charlesvestal/owntone-nfc/tests/test_controller.py

import datetime

import httpx
import pytest

from nfc_jukebox.cards import Card
from nfc_jukebox.config import Config
from nfc_jukebox.controller import Controller, State
from nfc_jukebox.owntone import is_airplay, is_local


class FakeClock:
    def __init__(self) -> None:
        self.now = 1000.0

    def __call__(self) -> float:
        return self.now

    def advance(self, seconds: float) -> None:
        self.now += seconds


class FakeWallClock:
    """The *second* time source: local wall-clock time, for "has 3am happened".

    Separate from FakeClock on purpose, exactly as in the controller: durations
    are measured on the monotonic clock, and only the question "which side of
    the reset hour are we on" is asked of this one. Tests drive it explicitly
    so nothing has to sleep or move the machine's clock.
    """

    def __init__(self, at: str = "2026-09-18 20:00") -> None:
        self.now = datetime.datetime.fromisoformat(at)

    def __call__(self) -> datetime.datetime:
        return self.now

    def set(self, at: str) -> None:
        self.now = datetime.datetime.fromisoformat(at)


class FakeOwnTone:
    """A stand-in for the REST client.

    The `type` strings are OwnTone's real ones, and the classification
    predicates are imported from the production module rather than re-guessed
    here: fakes that reimplement the thing under test are how the AirPlay
    release bug survived a green suite.
    """

    def __init__(self) -> None:
        self.calls: list[tuple] = []
        self.outputs = [
            {"id": "1", "type": "ALSA", "selected": True},
            {"id": "2", "type": "AirPlay 2", "selected": False},
        ]
        # The queue and the transport state are modelled because the resume
        # rule depends on both: the position lives in OwnTone's queue, and
        # "the side has run out" is only visible as the player stopping.
        self.queue = 0
        self.player = "stop"
        # Which album the queue holds, so a restart can recognise it.
        self.queue_album: str | None = None

    def _ids(self, predicate):
        return [o["id"] for o in self.outputs if predicate(o)]

    def selected_output_ids(self):
        return self._ids(lambda o: o["selected"])

    def airplay_output_ids(self):
        return self._ids(is_airplay)

    def local_output_ids(self):
        return self._ids(is_local)

    def all_output_ids(self):
        return self._ids(lambda o: True)

    def set_vinyl_playback_mode(self):
        self.calls.append(("set_vinyl_playback_mode",))

    def set_outputs(self, ids):
        self.calls.append(("set_outputs", tuple(ids)))
        for o in self.outputs:
            o["selected"] = o["id"] in ids

    def play_album(self, path):
        self.calls.append(("play_album", path))
        self.queue = 12
        self.queue_album = path
        self.player = "play"

    def play(self):
        self.calls.append(("play",))
        self.player = "play"

    def pause(self):
        self.calls.append(("pause",))
        self.player = "pause"

    def stop(self):
        self.calls.append(("stop",))
        self.player = "stop"

    def clear_queue(self):
        self.calls.append(("clear_queue",))
        self.queue = 0
        self.queue_album = None
        self.player = "stop"

    def queue_length(self):
        self.calls.append(("queue_length",))
        return self.queue

    def player_state(self):
        return {"state": self.player}

    def queue_holds_album(self, relative_path):
        return self.queue > 0 and self.queue_album == relative_path

    def finish_album(self):
        """What OwnTone looks like when the last track has played out."""
        self.player = "stop"


class FakeCards:
    def __init__(self, mapping):
        self._mapping = mapping

    def get(self, uid):
        return self._mapping.get(uid)


class FakeSnapshot:
    def __init__(self, initial=None):
        self.value = initial or []

    def load(self):
        return list(self.value)

    def save(self, ids):
        self.value = list(ids)


@pytest.fixture
def wall():
    return FakeWallClock()


@pytest.fixture
def ctx(wall):
    clock = FakeClock()
    owntone = FakeOwnTone()
    cards = FakeCards({
        "aaaa": Card(uid="aaaa", name="Blue", path="Miles Davis/Kind of Blue"),
        "bbbb": Card(uid="bbbb", name="Rumours", path="Fleetwood Mac/Rumours"),
        # Only ever used by _prime, which has to leave a *different* record on
        # the platter from the one the test under way is about.
        "cccc": Card(uid="cccc", name="Primer", path="Various/Primer"),
    })
    snapshot = FakeSnapshot()
    config = Config(grace_period_s=90.0)
    controller = Controller(owntone, cards, snapshot, config,
                            clock=clock, wall_clock=wall)
    return controller, owntone, snapshot, clock


def test_card_placed_starts_album(ctx):
    controller, owntone, _, _ = ctx
    controller.on_card_present("aaaa")
    assert ("play_album", "Miles Davis/Kind of Blue") in owntone.calls
    assert controller.state is State.PLAYING


def test_card_removed_pauses_immediately(ctx):
    controller, owntone, _, _ = ctx
    controller.on_card_present("aaaa")
    controller.on_card_removed()
    assert owntone.calls[-1] == ("pause",)
    assert controller.state is State.PAUSED


def test_same_card_replaced_at_once_resumes(ctx):
    controller, owntone, _, clock = ctx
    controller.on_card_present("aaaa")
    controller.on_card_removed()
    clock.advance(0.2)
    controller.on_card_present("aaaa")
    assert owntone.calls[-1] == ("play",)
    album_calls = [c for c in owntone.calls if c[0] == "play_album"]
    assert album_calls == [("play_album", "Miles Davis/Kind of Blue")]


def test_same_card_resumes_however_long_it_has_been_off(ctx):
    """Lifting a card is how you pause a record player, and pausing must not
    lose your place. The record stays on the platter until a different one is
    put on - so there is no window after which the same card starts over."""
    controller, owntone, _, clock = ctx
    controller.on_card_present("aaaa")
    controller.on_card_removed()
    clock.advance(3600.0)
    controller.tick()  # grace expired long ago; the outputs were released
    controller.on_card_present("aaaa")
    assert sum(1 for c in owntone.calls if c[0] == "play_album") == 1
    assert owntone.calls[-1] == ("play",)
    assert controller.state is State.PLAYING
    assert controller.now_playing == "Blue"


def test_a_resume_after_a_release_re_selects_the_speakers(ctx):
    """The release handed the HomePods back, so a resume has to take them
    again - otherwise the record comes back out of the wrong speaker."""
    controller, owntone, snapshot, clock = ctx
    _prime(controller, owntone, snapshot, clock)
    snapshot.save(["1", "2"])
    controller.on_card_present("aaaa")
    assert owntone.selected_output_ids() == ["1", "2"]

    controller.on_card_removed()
    clock.advance(91.0)
    controller.tick()
    assert owntone.selected_output_ids() == ["1"]  # HomePod handed back

    controller.on_card_present("aaaa")
    assert owntone.selected_output_ids() == ["1", "2"]
    assert controller.state is State.PLAYING


def test_different_card_switches_immediately(ctx):
    controller, owntone, _, _ = ctx
    controller.on_card_present("aaaa")
    controller.on_card_present("bbbb")
    assert ("play_album", "Fleetwood Mac/Rumours") in owntone.calls


def test_a_different_card_starts_from_track_one_not_where_it_left_off(ctx):
    """Only one record is on the platter at a time. Putting a different one on
    is what ends the first one's place."""
    controller, owntone, _, clock = ctx
    controller.on_card_present("aaaa")
    controller.on_card_removed()
    clock.advance(91.0)
    controller.tick()

    controller.on_card_present("bbbb")
    assert ("play_album", "Fleetwood Mac/Rumours") in owntone.calls

    controller.on_card_removed()
    clock.advance(91.0)
    controller.tick()
    owntone.calls.clear()

    controller.on_card_present("aaaa")  # back to the first record
    assert ("play_album", "Miles Davis/Kind of Blue") in owntone.calls
    assert ("play",) not in owntone.calls


def test_grace_expiry_releases_airplay_without_losing_the_place(ctx):
    """Releasing the speakers is the part that matters: the HomePods must go
    idle and become available to other senders. Stopping and clearing the
    queue would throw the position away, and the position is the whole point
    of the pause."""
    controller, owntone, _, clock = ctx
    owntone.outputs[1]["selected"] = True  # AirPlay selected
    controller.on_card_present("aaaa")
    controller.on_card_removed()
    clock.advance(91.0)
    controller.tick()
    assert owntone.selected_output_ids() == ["1"]  # AirPlay deselected
    assert ("stop",) not in owntone.calls
    assert ("clear_queue",) not in owntone.calls
    assert owntone.queue == 12  # the album is still loaded
    assert controller.state is State.IDLE


def test_a_finished_album_starts_over_on_the_next_tap(ctx):
    """A record that played its last groove has no place left to hold."""
    controller, owntone, _, clock = ctx
    controller.on_card_present("aaaa")

    owntone.finish_album()
    clock.advance(30.0)
    controller.tick()

    controller.on_card_removed()
    clock.advance(91.0)
    controller.tick()
    owntone.calls.clear()

    controller.on_card_present("aaaa")
    assert ("play_album", "Miles Davis/Kind of Blue") in owntone.calls
    assert ("play",) not in owntone.calls


def test_a_paused_album_is_not_mistaken_for_a_finished_one(ctx):
    """OwnTone reports `pause` for a card lifted mid-track and `stop` only
    when the queue has run out. Confusing the two would throw the place away
    on every lift."""
    controller, owntone, _, clock = ctx
    controller.on_card_present("aaaa")
    controller.on_card_removed()
    assert owntone.player_state()["state"] == "pause"
    clock.advance(30.0)
    controller.tick()
    owntone.calls.clear()

    controller.on_card_present("aaaa")
    assert ("play",) in owntone.calls
    assert not any(c[0] == "play_album" for c in owntone.calls)


def test_the_finished_check_is_not_run_on_every_tick(ctx):
    controller, owntone, _, clock = ctx
    controller.on_card_present("aaaa")
    polls = []
    owntone.player_state = lambda: (polls.append(1), {"state": "play"})[1]
    for _ in range(10):
        clock.advance(1.0)
        controller.tick()
    assert len(polls) <= 1


def test_a_stale_loaded_album_does_not_resume_into_an_empty_queue(ctx):
    """OwnTone restarting under us empties the queue while our memory of what
    is loaded survives. Resuming then would be silence, so the check is what
    OwnTone actually has, not what we remember."""
    controller, owntone, _, clock = ctx
    controller.on_card_present("aaaa")
    controller.on_card_removed()
    clock.advance(91.0)
    controller.tick()

    owntone.queue = 0  # OwnTone restarted; the queue went with it
    owntone.calls.clear()

    controller.on_card_present("aaaa")
    assert ("play_album", "Miles Davis/Kind of Blue") in owntone.calls
    assert controller.state is State.PLAYING


def test_a_failed_queue_check_starts_the_album_rather_than_risking_silence(ctx):
    controller, owntone, _, clock = ctx
    controller.on_card_present("aaaa")
    controller.on_card_removed()
    clock.advance(91.0)
    controller.tick()
    owntone.queue_length = _boom
    owntone.calls.clear()

    controller.on_card_present("aaaa")
    assert ("play_album", "Miles Davis/Kind of Blue") in owntone.calls
    assert controller.state is State.PLAYING


# --- start over ------------------------------------------------------------


def test_start_over_restarts_the_loaded_album(ctx):
    controller, owntone, _, clock = ctx
    controller.on_card_present("aaaa")
    controller.on_card_removed()
    clock.advance(91.0)
    controller.tick()
    owntone.calls.clear()

    assert controller.start_over() == "Blue"

    assert ("play_album", "Miles Davis/Kind of Blue") in owntone.calls
    assert controller.state is State.PLAYING
    assert controller.now_playing == "Blue"


def test_start_over_re_selects_the_speakers_too(ctx):
    controller, owntone, snapshot, clock = ctx
    _prime(controller, owntone, snapshot, clock)
    snapshot.save(["1", "2"])
    controller.on_card_present("aaaa")
    controller.on_card_removed()
    clock.advance(91.0)
    controller.tick()
    assert owntone.selected_output_ids() == ["1"]

    controller.start_over()

    assert owntone.selected_output_ids() == ["1", "2"]


def test_start_over_with_nothing_loaded_says_so(ctx):
    controller, owntone, _, _ = ctx
    with pytest.raises(LookupError):
        controller.start_over()
    assert not any(c[0] == "play_album" for c in owntone.calls)


def test_start_over_after_a_finished_album_has_nothing_to_restart(ctx):
    controller, owntone, _, clock = ctx
    controller.on_card_present("aaaa")
    owntone.finish_album()
    clock.advance(30.0)
    controller.tick()
    with pytest.raises(LookupError):
        controller.start_over()


def test_start_over_surfaces_an_owntone_failure(ctx):
    controller, owntone, _, _ = ctx
    controller.on_card_present("aaaa")
    owntone.play_album = _boom
    with pytest.raises(RuntimeError):
        controller.start_over()
    assert controller.last_error is not None


def test_start_over_mid_album_does_not_need_the_card_lifted(ctx):
    controller, owntone, _, _ = ctx
    controller.on_card_present("aaaa")
    owntone.calls.clear()
    controller.start_over()
    assert ("play_album", "Miles Davis/Kind of Blue") in owntone.calls
    assert controller.state is State.PLAYING


# --- the nightly reset -----------------------------------------------------
#
# An album left unfinished at midnight should not still be waiting mid-side at
# lunchtime the next day. The reset hour is a wall-clock question, which is why
# the controller carries a second, separate time source: the monotonic clock
# cannot answer "has 3am happened", and the wall clock must never be used for
# the grace period, where an NTP step would strand a paused card.


def test_an_album_loaded_last_night_starts_fresh_after_the_reset_hour(ctx, wall):
    controller, owntone, _, clock = ctx
    wall.set("2026-09-18 23:00")
    controller.on_card_present("aaaa")
    controller.on_card_removed()
    clock.advance(91.0)
    controller.tick()
    owntone.calls.clear()

    wall.set("2026-09-19 10:00")  # 3am has been and gone
    controller.on_card_present("aaaa")

    assert ("play_album", "Miles Davis/Kind of Blue") in owntone.calls
    assert ("play",) not in owntone.calls


def test_the_same_night_still_resumes_across_midnight(ctx, wall):
    controller, owntone, _, clock = ctx
    wall.set("2026-09-18 23:00")
    controller.on_card_present("aaaa")
    controller.on_card_removed()
    clock.advance(91.0)
    controller.tick()
    owntone.calls.clear()

    wall.set("2026-09-19 02:00")  # still the same evening, by the 3am rule
    controller.on_card_present("aaaa")

    assert ("play",) in owntone.calls
    assert not any(c[0] == "play_album" for c in owntone.calls)


def test_the_reset_hour_can_be_turned_off(ctx, wall):
    controller, owntone, snapshot, clock = ctx
    controller._config = Config(grace_period_s=90.0, resume_reset_hour=None)
    wall.set("2026-09-18 23:00")
    controller.on_card_present("aaaa")
    controller.on_card_removed()
    clock.advance(91.0)
    controller.tick()
    owntone.calls.clear()

    wall.set("2026-09-25 10:00")  # a week and seven 3ams later
    controller.on_card_present("aaaa")

    assert ("play",) in owntone.calls
    assert not any(c[0] == "play_album" for c in owntone.calls)


def test_the_reset_hour_does_not_interrupt_a_playing_album(ctx, wall):
    """It decides what the *next* tap does. A record playing through 3am keeps
    playing; nothing about the reset touches the transport."""
    controller, owntone, _, clock = ctx
    wall.set("2026-09-19 02:55")
    controller.on_card_present("aaaa")
    owntone.calls.clear()

    wall.set("2026-09-19 03:05")
    clock.advance(30.0)
    controller.tick()

    assert controller.state is State.PLAYING
    assert not any(c[0] in ("stop", "pause", "clear_queue") for c in owntone.calls)


def test_a_reset_that_passed_mid_album_only_bites_on_the_next_tap(ctx, wall):
    controller, owntone, _, clock = ctx
    wall.set("2026-09-19 02:55")
    controller.on_card_present("aaaa")
    controller.on_card_removed()
    clock.advance(91.0)
    controller.tick()
    owntone.calls.clear()

    wall.set("2026-09-19 03:05")
    controller.on_card_present("aaaa")

    assert ("play_album", "Miles Davis/Kind of Blue") in owntone.calls


def test_starting_an_album_after_the_reset_hour_sets_a_fresh_deadline(ctx, wall):
    """The clock that matters is when the album was loaded, not the calendar
    day: a record put on at 10am resumes all afternoon."""
    controller, owntone, _, clock = ctx
    wall.set("2026-09-19 10:00")
    controller.on_card_present("aaaa")
    controller.on_card_removed()
    clock.advance(91.0)
    controller.tick()
    owntone.calls.clear()

    wall.set("2026-09-19 22:00")
    controller.on_card_present("aaaa")

    assert ("play",) in owntone.calls
    assert not any(c[0] == "play_album" for c in owntone.calls)


def test_snapshot_restored_on_next_card(ctx):
    controller, owntone, snapshot, clock = ctx
    owntone.outputs[1]["selected"] = True
    controller.on_card_present("aaaa")
    controller.on_card_removed()
    clock.advance(91.0)
    controller.tick()
    assert snapshot.load() == ["1", "2"]
    controller.on_card_present("aaaa")
    assert owntone.selected_output_ids() == ["1", "2"]


def test_manual_airplay_selection_while_idle_is_not_clobbered(ctx):
    controller, owntone, snapshot, clock = ctx
    _prime(controller, owntone, snapshot, clock)  # we last selected local
    snapshot.save(["1"])
    owntone.outputs[1]["selected"] = True  # user picked AirPlay by hand
    controller.on_card_present("aaaa")
    # Assert the *absence of the write*, not the resulting state: the state was
    # set up two lines above, so asserting it would pass even if
    # _restore_outputs were replaced with `return`.
    assert not any(c[0] == "set_outputs" for c in owntone.calls)
    assert owntone.selected_output_ids() == ["1", "2"]


def test_manual_chromecast_selection_while_idle_is_not_clobbered(ctx):
    """A choice that is neither local nor AirPlay needs no special case: it
    differs from what we last selected, which is the whole test."""
    controller, owntone, snapshot, clock = ctx
    _prime(controller, owntone, snapshot, clock)
    owntone.outputs.append({"id": "7", "type": "Chromecast", "selected": True})
    owntone.outputs[0]["selected"] = False
    snapshot.save(["1"])
    controller.on_card_present("aaaa")
    assert not any(c[0] == "set_outputs" for c in owntone.calls)


def test_missing_saved_output_falls_back_to_local(ctx):
    controller, owntone, snapshot, clock = ctx
    # Past the first cycle, so the local-only selection is known to be ours
    # and the snapshot is what we act on. See _prime.
    _prime(controller, owntone, snapshot, clock)
    snapshot.save(["99"])  # HomePod no longer on the network
    controller.on_card_present("aaaa")
    # The fallback must be an actual write of the local outputs, not merely the
    # local-only selection the fixture already starts in.
    assert ("set_outputs", ("1",)) in owntone.calls
    assert owntone.selected_output_ids() == ["1"]
    assert controller.last_error is not None
    assert ("play_album", "Miles Davis/Kind of Blue") in owntone.calls
    assert controller.state is State.PLAYING


def test_release_selects_only_real_local_outputs(ctx):
    """A release must not hand the record to a Chromecast or to the HTTP
    stream just because they are not AirPlay."""
    controller, owntone, _, clock = ctx
    owntone.outputs += [
        {"id": "7", "type": "Chromecast", "selected": False},
        {"id": "8", "type": "streaming", "selected": False},
    ]
    owntone.outputs[1]["selected"] = True
    controller.on_card_present("aaaa")
    controller.on_card_removed()
    clock.advance(91.0)
    controller.tick()
    assert owntone.selected_output_ids() == ["1"]


def test_starting_an_album_forces_shuffle_and_repeat_off(ctx):
    """OwnTone persists shuffle across restarts and its UI has a one-click
    toggle. With shuffle on, `playback=start` picks a random track and the
    vinyl contract breaks invisibly."""
    controller, owntone, _, _ = ctx
    controller.on_card_present("aaaa")
    assert ("set_vinyl_playback_mode",) in owntone.calls
    order = [c[0] for c in owntone.calls]
    assert order.index("set_vinyl_playback_mode") < order.index("play_album")


def test_vinyl_mode_failure_still_plays(ctx):
    controller, owntone, _, _ = ctx
    owntone.set_vinyl_playback_mode = _boom
    controller.on_card_present("aaaa")
    assert ("play_album", "Miles Davis/Kind of Blue") in owntone.calls
    assert controller.state is State.PLAYING
    assert controller.last_error is not None


def test_last_error_is_cleared_by_a_successful_start(ctx):
    controller, owntone, _, _ = ctx
    controller.on_card_present("ffff")  # hotel key card
    assert controller.last_error is not None
    controller.on_card_present("aaaa")
    assert controller.state is State.PLAYING
    # Otherwise one stray tap sits on the admin status line forever.
    assert controller.last_error is None


def test_last_error_is_cleared_by_a_successful_resume(ctx):
    controller, owntone, _, clock = ctx
    controller.on_card_present("aaaa")
    controller.on_card_removed()
    controller.last_error = "stale"
    clock.advance(0.2)
    controller.on_card_present("aaaa")
    assert controller.state is State.PLAYING
    assert controller.last_error is None


def test_a_shrunken_selection_does_not_destroy_the_saved_choice(ctx):
    """The HomePod drops mid-album (Wi-Fi blip, or the documented
    `ANNOUNCE ... 400 Bad Request` self-deselect). OwnTone now reports local
    only. Saving that over the snapshot would forget the speaker for good."""
    controller, owntone, snapshot, clock = ctx
    snapshot.save(["1", "2"])
    owntone.outputs[1]["selected"] = True
    controller.on_card_present("aaaa")
    owntone.outputs[1]["selected"] = False  # the speaker drops off
    controller.on_card_removed()
    clock.advance(91.0)
    controller.tick()
    assert snapshot.load() == ["1", "2"]
    # Never silently: the operator gets told why the snapshot was kept.
    assert controller.last_error is not None


def test_a_repeated_shrink_is_taken_as_a_deliberate_change(ctx):
    """One shrink is a drop; the same shrink surviving a full restore cycle is
    the user really having chosen local-only, and must eventually stick."""
    controller, owntone, snapshot, clock = ctx
    snapshot.save(["1", "2"])
    owntone.outputs[1]["selected"] = True

    for _ in range(2):
        controller.on_card_present("aaaa")
        owntone.outputs[1]["selected"] = False  # user deselects it again
        controller.on_card_removed()
        clock.advance(91.0)
        controller.tick()

    assert snapshot.load() == ["1"]


def test_a_grown_selection_is_saved_immediately(ctx):
    controller, owntone, snapshot, clock = ctx
    snapshot.save(["1"])
    controller.on_card_present("aaaa")
    owntone.outputs[1]["selected"] = True  # user adds the HomePod mid-album
    controller.on_card_removed()
    clock.advance(91.0)
    controller.tick()
    assert snapshot.load() == ["1", "2"]


def test_unknown_card_is_ignored(ctx):
    controller, owntone, _, _ = ctx
    controller.on_card_present("ffff")
    assert not any(c[0] == "play_album" for c in owntone.calls)
    assert controller.last_error is not None
    assert controller.state is State.IDLE


def test_unknown_card_is_still_recorded_for_learn_mode(ctx):
    controller, _, _, _ = ctx
    controller.on_card_present("ffff")
    assert controller.last_seen_uid == "ffff"


def test_same_card_re_presented_while_playing_is_a_noop(ctx):
    """A double-fired present event for a still-seated card must not restart."""
    controller, owntone, _, clock = ctx
    controller.on_card_present("aaaa")
    before = list(owntone.calls)
    clock.advance(30.0)  # the card never left the platter
    controller.on_card_present("aaaa")
    assert owntone.calls == before
    assert controller.state is State.PLAYING
    assert controller.last_seen_uid == "aaaa"
    assert controller.last_seen_at == clock.now


def _boom(*_args, **_kwargs):
    """Stand-in for what owntone.py raises on any 4xx/5xx."""
    request = httpx.Request("PUT", "http://test:3689/api/player/play")
    raise httpx.HTTPStatusError(
        "500", request=request, response=httpx.Response(500, request=request)
    )


def test_play_album_failure_does_not_escape_and_is_recorded(ctx):
    controller, owntone, _, _ = ctx
    owntone.play_album = _boom
    controller.on_card_present("aaaa")
    assert controller.last_error is not None
    # Never claim PLAYING when playback demonstrably failed to start.
    assert controller.state is not State.PLAYING
    assert controller.now_playing is None


def test_resume_failure_does_not_escape(ctx):
    controller, owntone, _, clock = ctx
    controller.on_card_present("aaaa")
    controller.on_card_removed()
    clock.advance(0.2)
    owntone.play = _boom
    controller.on_card_present("aaaa")
    assert controller.last_error is not None
    assert controller.state is not State.PLAYING


def test_restore_outputs_failure_still_plays_locally(ctx):
    """A dead HomePod (still in OwnTone's list via cached mDNS, 500s on
    `/api/outputs/set`) must not make the box silent. The spec: play locally
    anyway and surface it. Output selection is best-effort; playback is the
    contract."""
    controller, owntone, _, _ = ctx
    owntone.selected_output_ids = _boom
    controller.on_card_present("aaaa")
    assert controller.last_error is not None
    assert ("play_album", "Miles Davis/Kind of Blue") in owntone.calls
    assert controller.state is State.PLAYING
    assert controller.now_playing == "Blue"
    # ...and having failed to work out the right outputs, fall back to local.
    assert ("set_outputs", ("1",)) in owntone.calls


def test_total_output_failure_still_plays(ctx):
    """Even the local fallback failing must not stop the record."""
    controller, owntone, _, _ = ctx
    owntone.selected_output_ids = _boom
    owntone.set_outputs = _boom
    controller.on_card_present("aaaa")
    assert ("play_album", "Miles Davis/Kind of Blue") in owntone.calls
    assert controller.state is State.PLAYING


def test_non_http_failure_is_contained(ctx):
    """A 200 with a non-JSON body (a reverse proxy, or OwnTone serving its SPA
    index) raises JSONDecodeError/KeyError, not httpx.HTTPError. It must not
    escape into the reader thread."""
    controller, owntone, _, _ = ctx

    def bad_shape(*_a, **_k):
        raise KeyError("outputs")

    owntone.selected_output_ids = bad_shape
    controller.on_card_present("aaaa")
    assert controller.last_error is not None
    assert controller.state is State.PLAYING


def test_playback_failure_of_an_unexpected_kind_is_contained(ctx):
    controller, owntone, _, _ = ctx

    def bad_shape(*_a, **_k):
        raise ValueError("Expecting value: line 1 column 1 (char 0)")

    owntone.play_album = bad_shape
    controller.on_card_present("aaaa")
    assert controller.last_error is not None
    assert controller.state is not State.PLAYING


def test_keyboard_interrupt_is_not_swallowed(ctx):
    """Containment is for OwnTone misbehaving, not for shutdown signals."""
    controller, owntone, _, _ = ctx

    def interrupted(*_a, **_k):
        raise KeyboardInterrupt

    owntone.play_album = interrupted
    with pytest.raises(KeyboardInterrupt):
        controller.on_card_present("aaaa")


def test_pause_failure_does_not_escape(ctx):
    controller, owntone, _, _ = ctx
    controller.on_card_present("aaaa")
    owntone.pause = _boom
    controller.on_card_removed()
    assert controller.last_error is not None
    # Still parked in PAUSED so the grace timer can release later.
    assert controller.state is State.PAUSED


def test_release_failure_does_not_escape(ctx):
    controller, owntone, _, clock = ctx
    controller.on_card_present("aaaa")
    controller.on_card_removed()
    # Handing the speakers back is the only OwnTone call a release still makes,
    # now that stopping and clearing would throw the position away.
    owntone.set_outputs = _boom
    clock.advance(91.0)
    controller.tick()
    assert controller.last_error is not None
    assert controller.state is State.IDLE


# --- output verification ---------------------------------------------------
#
# Every synchronous call at card-tap time can succeed and the box can still end
# up playing to the wrong speaker: an AirPlay 2 HomePod refuses pairing several
# seconds later, deselects itself, and OwnTone quietly falls back to the local
# soundcard. `state=play`, `last_error=None`, and the user is listening to the
# wrong thing. These tests pin the after-the-fact check that notices.


def _start_with_both_outputs(ctx):
    """Start an album with local + AirPlay selected, as the snapshot asks."""
    controller, owntone, snapshot, clock = ctx
    # Primed so that a *hand-picked* selection would be respected; this test
    # is about the snapshot being applied in the ordinary steady state.
    # See _prime.
    _prime(controller, owntone, snapshot, clock)
    snapshot.save(["1", "2"])
    controller.on_card_present("aaaa")
    assert owntone.selected_output_ids() == ["1", "2"]
    assert controller.last_error is None
    return controller, owntone, snapshot, clock


def test_intended_output_deselected_after_start_is_reported(ctx):
    """The observed defect: the HomePod deselects itself post-pairing and
    OwnTone falls back to local. Nothing synchronous can see it."""
    controller, owntone, _, clock = _start_with_both_outputs(ctx)

    owntone.outputs[1]["selected"] = False  # pairing refused, seconds later

    clock.advance(30.0)
    controller.tick()

    assert controller.state is State.PLAYING  # audio *is* playing, just wrong
    assert controller.last_error is not None
    assert "2" in controller.last_error


def test_intended_output_vanishing_after_start_is_reported(ctx):
    """An output gone from /api/outputs entirely is a different fault from one
    still listed and deselected, and must say so."""
    controller, owntone, _, clock = _start_with_both_outputs(ctx)

    del owntone.outputs[1]  # HomePod dropped off the network altogether

    clock.advance(30.0)
    controller.tick()

    assert controller.last_error is not None
    assert "2" in controller.last_error
    assert "no longer" in controller.last_error


def test_a_user_switching_speakers_mid_album_is_not_an_error(ctx):
    """Changing outputs in OwnTone's own web UI is a deliberate act. Picking a
    speaker we did not ask for is the fingerprint of a human doing it."""
    controller, owntone, _, clock = _start_with_both_outputs(ctx)
    owntone.outputs.append({"id": "7", "type": "Chromecast", "selected": False})

    owntone.set_outputs(["7"])  # user moves the record to the Chromecast

    clock.advance(30.0)
    controller.tick()

    assert controller.last_error is None
    assert controller.state is State.PLAYING


def test_a_user_switch_replaces_what_we_expect_to_stay_selected(ctx):
    """Having adopted the user's choice, we watch *that* instead."""
    controller, owntone, _, clock = _start_with_both_outputs(ctx)
    owntone.outputs.append({"id": "7", "type": "Chromecast", "selected": False})

    owntone.set_outputs(["7"])
    clock.advance(30.0)
    controller.tick()
    assert controller.last_error is None

    owntone.outputs[2]["selected"] = False  # now the Chromecast drops
    clock.advance(30.0)
    controller.tick()

    assert controller.last_error is not None
    assert "7" in controller.last_error


def test_a_mismatch_is_reported_once_not_every_tick(ctx):
    controller, owntone, _, clock = _start_with_both_outputs(ctx)
    owntone.outputs[1]["selected"] = False

    clock.advance(30.0)
    controller.tick()
    assert controller.last_error is not None

    controller.last_error = None
    for _ in range(5):
        clock.advance(30.0)
        controller.tick()

    assert controller.last_error is None


def test_outputs_are_not_polled_on_every_tick(ctx):
    """One HTTP round trip per second, forever, for a box that sits idle-ish
    all evening. The check is periodic, not per-tick."""
    controller, owntone, _, clock = _start_with_both_outputs(ctx)
    owntone.outputs[1]["selected"] = False

    polls = []
    real = owntone.selected_output_ids
    owntone.selected_output_ids = lambda: (polls.append(1), real())[1]

    for _ in range(10):
        clock.advance(1.0)
        controller.tick()

    assert len(polls) <= 1


def test_a_new_card_resets_the_intended_outputs(ctx):
    controller, owntone, snapshot, clock = _start_with_both_outputs(ctx)
    owntone.outputs[1]["selected"] = False
    clock.advance(30.0)
    controller.tick()
    assert controller.last_error is not None

    controller.on_card_present("bbbb")  # fresh record, outputs re-selected
    assert controller.last_error is None
    assert owntone.selected_output_ids() == ["1", "2"]

    owntone.outputs[1]["selected"] = False  # and it drops out again
    clock.advance(30.0)
    controller.tick()

    assert controller.last_error is not None
    assert "2" in controller.last_error


def test_no_output_check_once_the_record_is_released(ctx):
    controller, owntone, _, clock = _start_with_both_outputs(ctx)
    controller.on_card_removed()
    clock.advance(91.0)
    controller.tick()  # grace expiry: stop, clear, back to local
    assert controller.state is State.IDLE
    controller.last_error = None

    polls = []
    real = owntone.selected_output_ids
    owntone.selected_output_ids = lambda: (polls.append(1), real())[1]
    clock.advance(30.0)
    controller.tick()

    assert polls == []
    assert controller.last_error is None


def test_a_failed_output_check_does_not_escape(ctx):
    controller, owntone, _, clock = _start_with_both_outputs(ctx)
    owntone.selected_output_ids = _boom

    clock.advance(30.0)
    controller.tick()

    assert controller.last_error is not None
    assert controller.state is State.PLAYING


def test_a_hand_picked_output_is_watched_too(ctx):
    """Adopting the user's selection means we never wrote one; the thing they
    chose by hand is still what we intend to be hearing."""
    controller, owntone, snapshot, clock = ctx
    _prime(controller, owntone, snapshot, clock)
    snapshot.save(["1"])
    owntone.outputs[1]["selected"] = True  # user picked the HomePod while idle
    controller.on_card_present("aaaa")
    assert not any(c[0] == "set_outputs" for c in owntone.calls)

    owntone.outputs[1]["selected"] = False  # ...and it refuses to pair
    clock.advance(30.0)
    controller.tick()

    assert controller.last_error is not None
    assert "2" in controller.last_error


def test_owntones_own_fallback_to_local_is_not_mistaken_for_a_user_choice(ctx):
    """The exact shape seen on hardware: HomePods only, pairing refused, and
    OwnTone silently selects the ALSA output instead. A *gained* output is
    normally the fingerprint of a person at the web UI -- but not when the
    thing gained is the local soundcard, which is the one place OwnTone's own
    fallback ever lands."""
    controller, owntone, snapshot, clock = ctx
    snapshot.save(["2"])  # HomePods only; nothing local wanted
    owntone.outputs[0]["selected"] = False
    controller.on_card_present("aaaa")
    assert owntone.selected_output_ids() == ["2"]

    owntone.outputs[1]["selected"] = False  # HomePod refuses to pair...
    owntone.outputs[0]["selected"] = True   # ...and OwnTone falls back

    clock.advance(30.0)
    controller.tick()

    assert controller.last_error is not None
    assert "2" in controller.last_error


def test_management_mode_identifies_cards_without_playing(ctx):
    # Registering a stack of cards while each tap starts an album is the wrong
    # experience, especially with speakers in a living room.
    controller, owntone, _, _ = ctx
    controller.set_management_mode(True)
    owntone.calls.clear()

    controller.on_card_present("aaaa")

    assert controller.last_seen_uid == "aaaa"
    assert not any(c[0] == "play_album" for c in owntone.calls)
    assert not any(c[0] == "play" for c in owntone.calls)
    assert controller.state is State.IDLE


def test_management_mode_still_learns_unregistered_cards(ctx):
    controller, _, _, _ = ctx
    controller.set_management_mode(True)
    controller.on_card_present("ffff")
    assert controller.last_seen_uid == "ffff"
    assert controller.last_error is not None


def test_management_mode_clears_the_error_for_a_known_card(ctx):
    controller, _, _, _ = ctx
    controller.set_management_mode(True)
    controller.on_card_present("ffff")
    assert controller.last_error is not None
    controller.on_card_present("aaaa")
    assert controller.last_error is None


def test_enabling_management_mode_leaves_playback_alone(ctx):
    # Management mode governs what a card read *means* -- identification only,
    # never play, pause or a switch of record. It is not about having a quiet
    # box to register against, which is why it no longer stops the music.
    controller, owntone, _, _ = ctx
    controller.on_card_present("aaaa")
    assert controller.state is State.PLAYING
    owntone.calls.clear()

    controller.set_management_mode(True)

    assert not any(c[0] in ("stop", "clear_queue", "pause")
                   for c in owntone.calls)
    assert controller.state is State.PLAYING
    assert controller.now_playing is not None


def test_leaving_management_mode_does_not_disturb_playback_either(ctx):
    controller, owntone, _, _ = ctx
    controller.on_card_present("aaaa")
    controller.set_management_mode(True)
    owntone.calls.clear()

    controller.set_management_mode(False)

    assert not any(c[0] in ("stop", "clear_queue", "pause")
                   for c in owntone.calls)
    assert controller.state is State.PLAYING


def test_management_mode_ignores_card_removal(ctx):
    controller, owntone, _, _ = ctx
    controller.set_management_mode(True)
    owntone.calls.clear()
    controller.on_card_removed()
    assert not any(c[0] == "pause" for c in owntone.calls)


def test_leaving_management_mode_restores_normal_playback(ctx):
    controller, owntone, _, _ = ctx
    controller.set_management_mode(True)
    controller.set_management_mode(False)
    owntone.calls.clear()
    controller.on_card_present("aaaa")
    assert ("play_album", "Miles Davis/Kind of Blue") in owntone.calls
    assert controller.state is State.PLAYING


# --- who changed the selection? --------------------------------------------
#
# The user picks speakers in OwnTone's own web UI; the jukebox does not
# duplicate that control. All it has to do is tell "the user changed this" from
# "this is the state we ourselves left behind at the last release", so that a
# deliberate choice is never overridden -- in either direction.


def _prime(controller, owntone, snapshot, clock):
    """Run one full card cycle so the controller has a record of what it set.

    Deliberately with a card no other test uses: a cycle leaves that record on
    the platter, and priming with the test's own card would turn its next tap
    into a resume.

    Fresh out of the box it has none, so it cannot tell a hand-picked
    selection from the state a previous run left behind, and applies the
    snapshot instead (see
    test_first_card_after_a_restart_restores_the_snapshot). Tests about
    honouring a user's own choice need to be past that first cycle. The empty
    snapshot keeps the cycle itself from tripping the shrink policy.
    """
    snapshot.value = []
    controller.on_card_present("cccc")
    controller.on_card_removed()
    clock.advance(91.0)
    controller.tick()
    owntone.calls.clear()
    controller.last_error = None


def test_first_card_after_a_restart_restores_the_snapshot(ctx):
    """The snapshot exists precisely to carry the speaker choice across a
    restart, so the first card after one must apply it.

    This deliberately overrides whatever OwnTone reports as selected. After a
    restart that selection is not evidence of anything: it is either the state
    a previous run left behind at release (local), or a row OwnTone persisted
    on its last clean shutdown. Deferring to it meant the first record of the
    evening played out of the Pi's headphone jack instead of the HomePods,
    which is the one thing the snapshot was built to prevent.

    The competing case -- a user deliberately picking the local output because
    they want headphones -- is still honoured from the second card on, once we
    have a record to compare against. See
    test_user_switching_to_local_while_idle_is_not_clobbered.
    """
    controller, owntone, snapshot, _ = ctx
    snapshot.save(["2"])  # a HomePod choice that survived the reboot

    controller.on_card_present("aaaa")

    assert owntone.selected_output_ids() == ["2"]
    assert controller.state is State.PLAYING
    # The snapshot is still not *adopted* from a selection we cannot vouch
    # for -- it is the thing being applied, and comes through unchanged.
    assert snapshot.load() == ["2"]


def test_first_card_after_a_restart_with_no_snapshot_leaves_things_alone(ctx):
    """Nothing saved means nothing to restore, and selecting nothing would
    guarantee silence. Whatever OwnTone has stays, and the record plays."""
    controller, owntone, snapshot, _ = ctx
    snapshot.value = []

    controller.on_card_present("aaaa")

    assert not any(c[0] == "set_outputs" for c in owntone.calls)
    assert owntone.selected_output_ids() == ["1"]
    assert controller.state is State.PLAYING


def test_user_switching_to_local_while_idle_is_not_clobbered(ctx):
    """The reported bug. The snapshot holds a HomePod; the user goes to
    OwnTone's UI while nothing is playing and picks the local output because
    they want headphones. The next card must not fling the sound back onto the
    HomePod."""
    controller, owntone, snapshot, clock = ctx
    _prime(controller, owntone, snapshot, clock)
    snapshot.save(["2"])
    controller.on_card_present("aaaa")
    assert owntone.selected_output_ids() == ["2"]
    controller.on_card_removed()  # record off the platter, nothing playing
    owntone.set_outputs(["1"])    # user picks local in OwnTone's web UI
    owntone.calls.clear()

    controller.on_card_present("bbbb")

    assert not any(c[0] == "set_outputs" for c in owntone.calls)
    assert owntone.selected_output_ids() == ["1"]
    # The new choice becomes the thing we remember for the release cycle.
    assert snapshot.load() == ["1"]


def test_user_switching_to_airplay_while_idle_is_still_respected(ctx):
    """The mirror of the case above, and the one the old guard rail already
    got right. It must keep working."""
    controller, owntone, snapshot, clock = ctx
    _prime(controller, owntone, snapshot, clock)
    snapshot.save(["1"])
    owntone.set_outputs(["1", "2"])  # user adds the HomePod by hand
    owntone.calls.clear()

    controller.on_card_present("aaaa")

    assert not any(c[0] == "set_outputs" for c in owntone.calls)
    assert owntone.selected_output_ids() == ["1", "2"]
    assert snapshot.load() == ["1", "2"]


def test_an_untouched_selection_is_restored_from_the_snapshot(ctx):
    """Nobody has been at the web UI since we selected local at release, so
    the saved choice is still the user's most recent word on the subject."""
    controller, owntone, snapshot, clock = ctx
    _prime(controller, owntone, snapshot, clock)
    snapshot.save(["1", "2"])

    controller.on_card_present("aaaa")

    assert ("set_outputs", ("1", "2")) in owntone.calls
    assert owntone.selected_output_ids() == ["1", "2"]


def test_the_local_fallback_at_card_start_counts_as_ours(ctx):
    """We set the outputs in two places, and both must update the record: a
    fallback that is not remembered looks like a user edit on the next card,
    and the snapshot would never be restored again."""
    controller, owntone, snapshot, clock = ctx
    _prime(controller, owntone, snapshot, clock)
    snapshot.save(["1", "2"])
    real = owntone.set_outputs
    owntone.set_outputs = _boom
    controller.on_card_present("aaaa")  # restore fails; falls back to local
    owntone.set_outputs = real
    owntone.set_outputs(["1"])          # the fallback that did not land
    controller.on_card_removed()
    clock.advance(91.0)
    controller.tick()
    controller.last_error = None
    owntone.calls.clear()

    controller.on_card_present("aaaa")

    assert ("set_outputs", ("1", "2")) in owntone.calls


def test_a_dropped_speaker_is_not_mistaken_for_a_deliberate_change(ctx):
    """A HomePod that deselects itself mid-album is a fault, not a choice. The
    next card must re-select it rather than treat local-only as the user's new
    intent -- and the snapshot must survive."""
    controller, owntone, snapshot, clock = ctx
    _prime(controller, owntone, snapshot, clock)
    snapshot.save(["1", "2"])
    controller.on_card_present("aaaa")
    assert owntone.selected_output_ids() == ["1", "2"]

    owntone.outputs[1]["selected"] = False  # pairing refused, seconds later
    clock.advance(30.0)
    controller.tick()
    assert controller.last_error is not None  # reported, once
    controller.last_error = None

    controller.on_card_removed()
    clock.advance(91.0)
    controller.tick()
    assert snapshot.load() == ["1", "2"]  # the shrink policy holds the line
    controller.last_error = None

    controller.on_card_present("bbbb")

    assert owntone.selected_output_ids() == ["1", "2"]
    assert snapshot.load() == ["1", "2"]


def test_no_outputs_selected_falls_through_to_the_snapshot(ctx):
    """An empty selection is a broken state, not a choice.

    "Leave a selection alone" protects a deliberate choice. Nothing selected
    is not one - it guarantees silence, which the design forbids - so the
    snapshot is restored instead. Observed for real: OwnTone came up with no
    speakers selected at all, and without this a card would have played to
    nothing.
    """
    controller, owntone, snapshot, _ = ctx
    snapshot.save(["1", "2"])
    for output in owntone.outputs:
        output["selected"] = False
    assert owntone.selected_output_ids() == []

    controller.on_card_present("aaaa")

    assert owntone.selected_output_ids() == ["1", "2"]
    assert ("play_album", "Miles Davis/Kind of Blue") in owntone.calls


# --- restarting the service under a running OwnTone -------------------------
#
# OwnTone outlives this service, so a redeploy leaves the record still turning.
# The controller used to wake with no memory, treat the seated card as new, and
# clear the queue to start side one again -- which is not what "restart the
# jukebox service" should mean to someone listening to it.


def _restarted(owntone, wall):
    """A fresh controller over an OwnTone that never stopped."""
    cards = FakeCards({
        "aaaa": Card(uid="aaaa", name="Blue", path="Miles Davis/Kind of Blue"),
        "bbbb": Card(uid="bbbb", name="Rumours", path="Fleetwood Mac/Rumours"),
    })
    return Controller(owntone, cards, FakeSnapshot(), Config(grace_period_s=90.0),
                      clock=FakeClock(), wall_clock=wall)


def test_a_restart_adopts_the_album_owntone_is_still_playing(ctx, wall):
    controller, owntone, _, _ = ctx
    controller.on_card_present("aaaa")
    assert controller.state is State.PLAYING

    fresh = _restarted(owntone, wall)
    owntone.calls.clear()
    fresh.on_card_present("aaaa")           # the card never left the platter

    assert not any(c[0] in ("play_album", "clear_queue", "stop")
                   for c in owntone.calls), owntone.calls
    assert fresh.state is State.PLAYING
    assert fresh.now_playing == "Blue"


def test_a_restart_resumes_an_album_owntone_had_paused(ctx, wall):
    controller, owntone, _, _ = ctx
    controller.on_card_present("aaaa")
    owntone.pause()

    fresh = _restarted(owntone, wall)
    owntone.calls.clear()
    fresh.on_card_present("aaaa")

    assert ("play",) in owntone.calls
    assert not any(c[0] == "play_album" for c in owntone.calls)
    assert fresh.state is State.PLAYING


def test_a_restart_with_a_different_card_starts_that_album(ctx, wall):
    """Adoption is only ever for the record actually on the turntable."""
    controller, owntone, _, _ = ctx
    controller.on_card_present("aaaa")

    fresh = _restarted(owntone, wall)
    owntone.calls.clear()
    fresh.on_card_present("bbbb")

    assert ("play_album", "Fleetwood Mac/Rumours") in owntone.calls


def test_a_restart_with_nothing_playing_starts_the_album(ctx, wall):
    controller, owntone, _, _ = ctx
    fresh = _restarted(owntone, wall)
    fresh.on_card_present("aaaa")
    assert ("play_album", "Miles Davis/Kind of Blue") in owntone.calls


def test_only_the_first_card_after_a_restart_can_adopt(ctx, wall):
    """A finished album also leaves no loaded card, and adopting there would
    resume a record that has already played out."""
    controller, owntone, _, _ = ctx
    fresh = _restarted(owntone, wall)
    fresh.on_card_present("aaaa")            # uses up the one adoption attempt
    owntone.calls.clear()

    fresh.on_card_present("bbbb")
    assert ("play_album", "Fleetwood Mac/Rumours") in owntone.calls


# --- scans from a reader that is not the jukebox's own ----------------------
#
# Registering 54 albums kneeling next to the box is a worse afternoon than
# doing it at a desk. A scan from elsewhere identifies a card and nothing
# else -- the same contract management mode already has.


def test_a_noted_scan_identifies_without_playing(ctx):
    controller, owntone, _, _ = ctx
    controller.note_scan("aaaa")
    assert controller.last_seen_uid == "aaaa"
    assert not owntone.calls
    assert controller.state is State.IDLE


def test_a_noted_scan_never_disturbs_a_playing_record(ctx):
    controller, owntone, _, _ = ctx
    controller.on_card_present("aaaa")
    owntone.calls.clear()

    controller.note_scan("bbbb")             # a different album entirely

    assert not owntone.calls
    assert controller.state is State.PLAYING
    assert controller.last_seen_uid == "bbbb"


def test_a_noted_scan_learns_an_unregistered_card(ctx):
    controller, _, _, _ = ctx
    controller.note_scan("ffff")
    assert controller.last_seen_uid == "ffff"
    assert "ffff" in (controller.last_error or "")


def test_a_noted_scan_clears_the_error_for_a_known_card(ctx):
    controller, _, _, _ = ctx
    controller.note_scan("ffff")
    controller.note_scan("aaaa")
    assert controller.last_error is None


def test_a_noted_scan_is_normalised(ctx):
    """The desk reader may format the UID differently."""
    controller, _, _, _ = ctx
    controller.note_scan("AA:AA")
    assert controller.last_seen_uid == "aaaa"


def test_lifting_the_card_after_the_side_ran_out_does_not_pause(ctx):
    """OwnTone answers 500 to a pause when there is nothing to pause.

    `_check_finished` leaves `state` PLAYING on purpose when the side runs
    out - that is what keeps a re-announced card a no-op - and only forgets
    the loaded record. Lifting the card then paused a player that had already
    stopped, and OwnTone rejects that with a 500. Seen twice on the box:

        web: Error pausing playback.
        web: JSON api request failed with error code 500 (/api/player/pause)

    The cost is not the failed call, which is caught. It is that the end of a
    record puts a red error on the admin page, and leaves the controller
    believing it paused something.
    """
    controller, owntone, _, clock = ctx
    controller.on_card_present("aaaa")
    owntone.finish_album()
    clock.advance(30.0)
    controller.tick()
    owntone.calls.clear()

    controller.on_card_removed()

    assert ("pause",) not in owntone.calls, \
        "paused a player that had already stopped"
    assert controller.last_error is None, \
        "the end of a record is not an error worth showing"
    # The speakers must still be let go on the usual grace timer.
    assert controller.state is State.PAUSED


def test_lifting_the_card_mid_record_still_pauses(ctx):
    """The guard above must not cost the ordinary lift its pause."""
    controller, owntone, _, clock = ctx
    controller.on_card_present("aaaa")
    owntone.calls.clear()

    controller.on_card_removed()

    assert ("pause",) in owntone.calls
    assert controller.state is State.PAUSED


def test_a_speaker_that_vanished_is_never_taken_as_a_deliberate_change(ctx):
    """A drop and a deselect are only indistinguishable while the output is
    still *there*.

    `_check_outputs` already separates the two: an output missing from
    OwnTone's list entirely is `vanished`, one present but unselected is
    `deselected`. Deselecting in the web UI leaves the speaker listed. Only a
    fault removes it. So a shrink whose missing members are gone from the list
    cannot be somebody's choice, however many times it repeats, and must never
    be allowed to overwrite the saved pair.

    Found on the box 2026-09-21: a night of Wi-Fi trouble repeatedly took
    HomePod Right out of OwnTone's list, the repeat-shrink rule read that as
    intent, and the snapshot was rewritten to Left only - so the next card
    restored one speaker and the record played in mono with nothing to say why.
    """
    controller, owntone, snapshot, clock = ctx
    snapshot.save(["1", "2"])
    owntone.outputs[1]["selected"] = True

    # Gone from the list, not merely unselected - and it STAYS gone, which is
    # what a speaker off the network actually does. Bringing it back between
    # cycles resets the shrink counter and hides the bug entirely.
    owntone.outputs[:] = [o for o in owntone.outputs if o["id"] != "2"]

    for _ in range(3):
        controller.on_card_present("aaaa")
        controller.on_card_removed()
        clock.advance(91.0)
        controller.tick()

    assert snapshot.load() == ["1", "2"], (
        "a speaker that vanished from OwnTone must not be forgotten, "
        "however often it happens"
    )


def test_a_vanished_speaker_is_re_selected_when_it_comes_back(ctx):
    """A speaker off the network is not a speaker refusing to pair.

    `_check_outputs` stops watching after reporting a loss, on the reasoning
    that re-selecting a receiver which just refused pairing will only refuse
    again. True for a `deselected` one - it is still listed, and it said no.
    A `vanished` one never said anything: it fell off the network. Those come
    back, and re-selecting on the way back converges instead of looping.

    Without this, a HomePod that blips mid-record leaves the rest of the side
    playing in mono, and the only way to get stereo back is to lift the card.
    """
    controller, owntone, _, clock = _start_with_both_outputs(ctx)

    gone = owntone.outputs.pop(1)          # off the network altogether
    clock.advance(30.0)
    controller.tick()
    assert "no longer" in (controller.last_error or "")

    owntone.calls.clear()
    gone["selected"] = False
    owntone.outputs.append(gone)           # and back again
    clock.advance(30.0)
    controller.tick()

    assert any(c[0] == "set_outputs" for c in owntone.calls), \
        "did not re-select the speaker when it returned"
    assert owntone.selected_output_ids() == ["1", "2"]
    assert controller.last_error is None


def test_a_receiver_that_refused_to_pair_is_not_retried(ctx):
    """The other half of the rule, and the reason it is not simply "retry".

    A receiver still in OwnTone's list that deselected itself has refused.
    Asking again produces the same refusal, so this must stay a single report
    rather than becoming a loop that never converges.
    """
    controller, owntone, _, clock = _start_with_both_outputs(ctx)

    owntone.outputs[1]["selected"] = False   # listed, but refused to pair
    clock.advance(30.0)
    controller.tick()
    assert "deselected themselves" in (controller.last_error or "")

    owntone.calls.clear()
    clock.advance(30.0)
    controller.tick()
    assert not any(c[0] == "set_outputs" for c in owntone.calls), \
        "retried a receiver that had already refused"


def test_a_vanished_speaker_is_reported_once_while_it_stays_away(ctx):
    """Keeping the watch alive must not turn one HomePod's absence into a
    warning every interval for the rest of the side."""
    controller, owntone, _, clock = _start_with_both_outputs(ctx)

    owntone.outputs.pop(1)
    clock.advance(30.0)
    controller.tick()
    controller.last_error = None            # operator has seen it

    for _ in range(3):
        clock.advance(30.0)
        controller.tick()

    assert controller.last_error is None, "re-reported a speaker already known gone"
